anirban185/MeteoNode/Hardware/MeteoNode.kicad_sch

## KiCad design Hardware/MeteoNode.kicad_sch (2026-06-10)

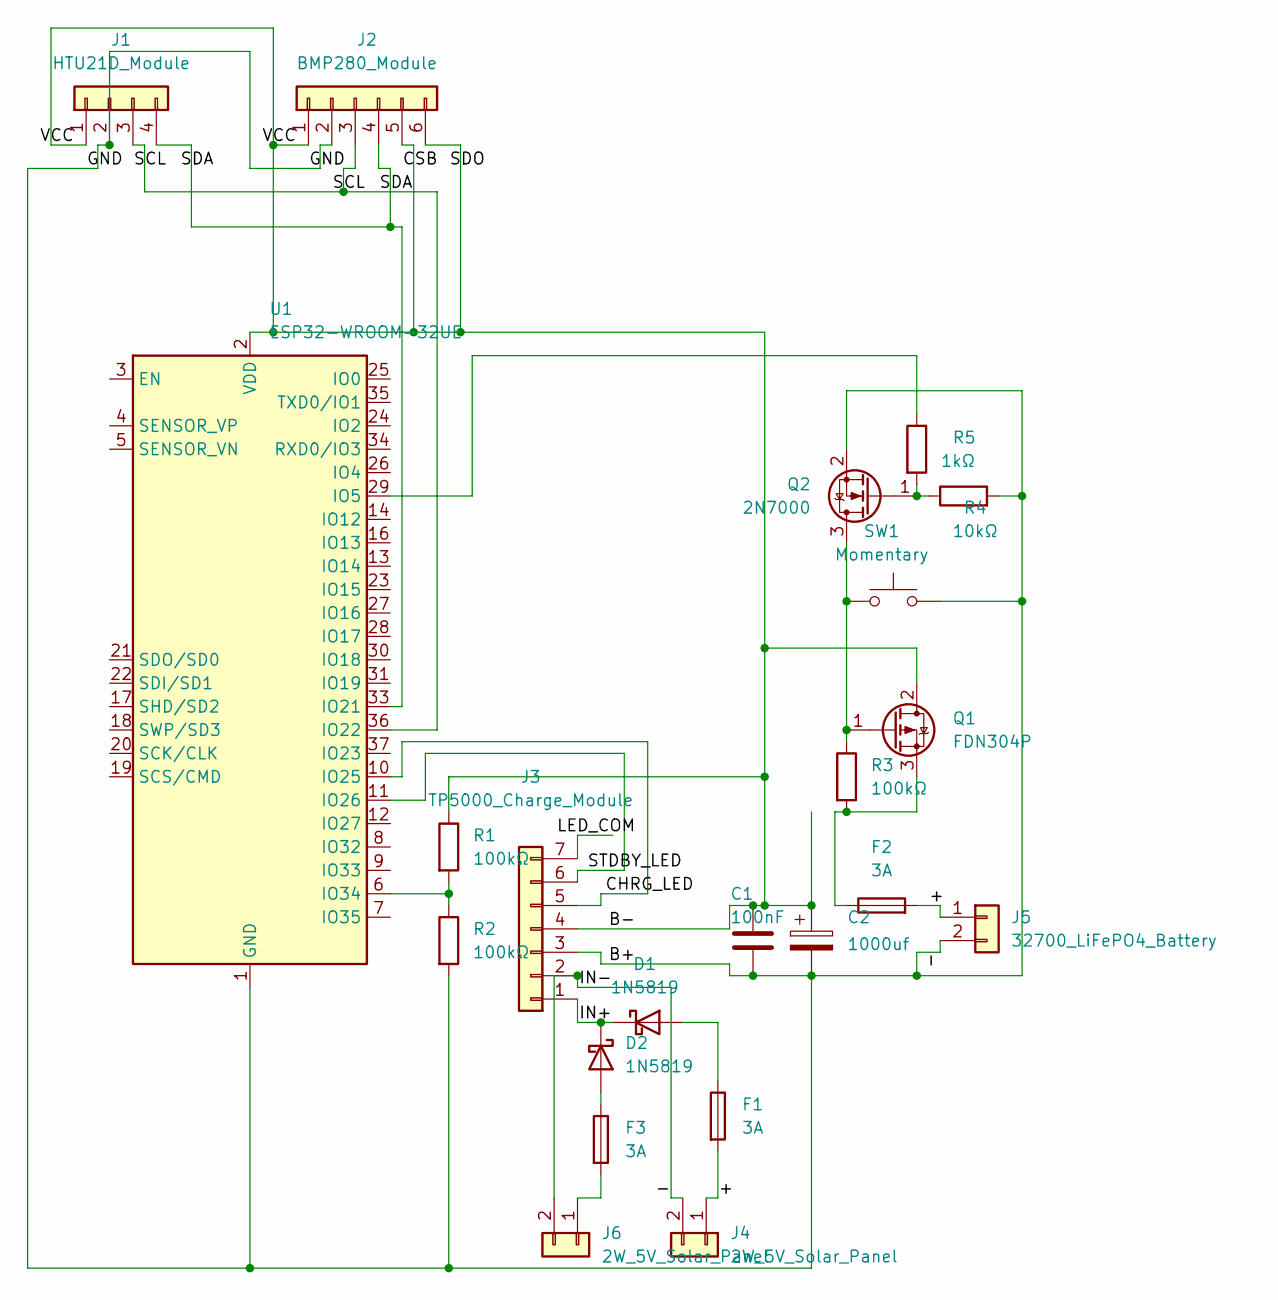
[picture p11: schematic MeteoNode.kicad_sch]

Parts:
C1: 100nF
C2: 1000uf
D1, D2: 1N5819
F1, F2, F3: 3A
J1: HTU21D_Module
J2: BMP280_Module
J3: TP5000_Charge_Module
J4, J6: 2W_5V_Solar_Panel
J5: 32700_LiFePO4_Battery
Q1: FDN304P
Q2: 2N7000
R1, R2, R3: 100kΩ
R4: 10kΩ
R5: 1kΩ
SW1: Momentary
U1: ESP32-WROOM-32UE; ESP32-WROOM-32U

Connections:
+: F1.2, F2.2, J4.1, J5.1
-: C1.2, C2.2, J1.2, J2.2, J3.2, J3.3, J4.2, J5.2, J6.2, Q2.2 (S), R2.2, R4.2, SW1.2, U1.1 (GND), U1.15 (GND), U1.38 (GND), U1.39 (GND)
B-: C1.1, C2.1, J1.1, J2.1, J2.5, J2.6, J3.4, Q1.2 (D), R1.1, U1.2 (VDD)
IN+: D1.1 (K), D2.1 (K), J3.1
unnamed: D1.2 (A), F1.1
unnamed: D2.2 (A), F3.1
unnamed: F2.1, Q1.3 (S), R3.2
unnamed: F3.2, J6.1
unnamed: J1.4, J2.4, U1.33 (IO21)
unnamed: J3.5, U1.10 (IO25)
unnamed: J3.6, U1.11 (IO26)
unnamed: Q1.1 (G), Q2.3 (D), R3.1, SW1.1
unnamed: Q2.1 (G), R4.1, R5.2
unnamed: R1.2, R2.1, U1.6 (IO34)
unnamed: R5.1, U1.29 (IO5)
SCL: J1.3, J2.3, U1.36 (IO22)
